daparker2/blastit/FPGA/controller/synthesis/submodules/controller_mm_interconnect_0_rsp_xbar_mux_001.sv

// (C) 2001-2013 Altera Corporation. All rights reserved.
// Your use of Altera Corporation's design tools, logic functions and other 
// software and tools, and its AMPP partner logic functions, and any output 
// files any of the foregoing (including device programming or simulation 
// files), and any associated documentation or information are expressly subject 
// to the terms and conditions of the Altera Program License Subscription 
// Agreement, Altera MegaCore Function License Agreement, or other applicable 
// license agreement, including, without limitation, that your use is for the 
// sole purpose of programming logic devices manufactured by Altera and sold by 
// Altera or its authorized distributors.  Please refer to the applicable 
// agreement for further details.


// $Id: //acds/rel/13.1/ip/merlin/altera_merlin_multiplexer/altera_merlin_multiplexer.sv.terp#1 $
// $Revision: #1 $
// $Date: 2013/08/11 $
// $Author: swbranch $

// ------------------------------------------
// Merlin Multiplexer
// ------------------------------------------

`timescale 1 ns / 1 ns


// ------------------------------------------
// Generation parameters:
//   output_name:         controller_mm_interconnect_0_rsp_xbar_mux_001
//   NUM_INPUTS:          49
//   ARBITRATION_SHARES:  1 1 1 1 1 1 1 1 1 1 1 1 1 1 1 1 1 1 1 1 1 1 1 1 1 1 1 1 1 1 1 1 1 1 1 1 1 1 1 1 1 1 1 1 1 1 1 1 1
//   ARBITRATION_SCHEME   "no-arb"
//   PIPELINE_ARB:        0
//   PKT_TRANS_LOCK:      57 (arbitration locking enabled)
//   ST_DATA_W:           99
//   ST_CHANNEL_W:        49
// ------------------------------------------

module controller_mm_interconnect_0_rsp_xbar_mux_001
(
    // ----------------------
    // Sinks
    // ----------------------
    input                       sink0_valid,
    input [99-1   : 0]  sink0_data,
    input [49-1: 0]  sink0_channel,
    input                       sink0_startofpacket,
    input                       sink0_endofpacket,
    output                      sink0_ready,

    input                       sink1_valid,
    input [99-1   : 0]  sink1_data,
    input [49-1: 0]  sink1_channel,
    input                       sink1_startofpacket,
    input                       sink1_endofpacket,
    output                      sink1_ready,

    input                       sink2_valid,
    input [99-1   : 0]  sink2_data,
    input [49-1: 0]  sink2_channel,
    input                       sink2_startofpacket,
    input                       sink2_endofpacket,
    output                      sink2_ready,

    input                       sink3_valid,
    input [99-1   : 0]  sink3_data,
    input [49-1: 0]  sink3_channel,
    input                       sink3_startofpacket,
    input                       sink3_endofpacket,
    output                      sink3_ready,

    input                       sink4_valid,
    input [99-1   : 0]  sink4_data,
    input [49-1: 0]  sink4_channel,
    input                       sink4_startofpacket,
    input                       sink4_endofpacket,
    output                      sink4_ready,

    input                       sink5_valid,
    input [99-1   : 0]  sink5_data,
    input [49-1: 0]  sink5_channel,
    input                       sink5_startofpacket,
    input                       sink5_endofpacket,
    output                      sink5_ready,

    input                       sink6_valid,
    input [99-1   : 0]  sink6_data,
    input [49-1: 0]  sink6_channel,
    input                       sink6_startofpacket,
    input                       sink6_endofpacket,
    output                      sink6_ready,

    input                       sink7_valid,
    input [99-1   : 0]  sink7_data,
    input [49-1: 0]  sink7_channel,
    input                       sink7_startofpacket,
    input                       sink7_endofpacket,
    output                      sink7_ready,

    input                       sink8_valid,
    input [99-1   : 0]  sink8_data,
    input [49-1: 0]  sink8_channel,
    input                       sink8_startofpacket,
    input                       sink8_endofpacket,
    output                      sink8_ready,

    input                       sink9_valid,
    input [99-1   : 0]  sink9_data,
    input [49-1: 0]  sink9_channel,
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

    input                       sink44_valid,
    input [99-1   : 0]  sink44_data,
    input [49-1: 0]  sink44_channel,
    input                       sink44_startofpacket,
    input                       sink44_endofpacket,
    output                      sink44_ready,

    input                       sink45_valid,
    input [99-1   : 0]  sink45_data,
    input [49-1: 0]  sink45_channel,
    input                       sink45_startofpacket,
    input                       sink45_endofpacket,
    output                      sink45_ready,

    input                       sink46_valid,
    input [99-1   : 0]  sink46_data,
    input [49-1: 0]  sink46_channel,
    input                       sink46_startofpacket,
    input                       sink46_endofpacket,
    output                      sink46_ready,

    input                       sink47_valid,
    input [99-1   : 0]  sink47_data,
    input [49-1: 0]  sink47_channel,
    input                       sink47_startofpacket,
    input                       sink47_endofpacket,
    output                      sink47_ready,

    input                       sink48_valid,
    input [99-1   : 0]  sink48_data,
    input [49-1: 0]  sink48_channel,
    input                       sink48_startofpacket,
    input                       sink48_endofpacket,
    output                      sink48_ready,


    // ----------------------
    // Source
    // ----------------------
    output                      src_valid,
    output [99-1    : 0] src_data,
    output [49-1 : 0] src_channel,
    output                      src_startofpacket,
    output                      src_endofpacket,
    input                       src_ready,

    // ----------------------
    // Clock & Reset
    // ----------------------
    input clk,
    input reset
);
    localparam PAYLOAD_W        = 99 + 49 + 2;
    localparam NUM_INPUTS       = 49;
    localparam SHARE_COUNTER_W  = 1;
    localparam PIPELINE_ARB     = 0;
    localparam ST_DATA_W        = 99;
    localparam ST_CHANNEL_W     = 49;
    localparam PKT_TRANS_LOCK   = 57;

    // ------------------------------------------
    // Signals
    // ------------------------------------------
    wire [NUM_INPUTS - 1 : 0] request;
    wire [NUM_INPUTS - 1 : 0] valid;
    wire [NUM_INPUTS - 1 : 0] grant;
    wire [NUM_INPUTS - 1 : 0] next_grant;
    reg  [NUM_INPUTS - 1 : 0] saved_grant;
    reg  [PAYLOAD_W - 1 : 0]  src_payload;
    wire                      last_cycle;
    reg                       packet_in_progress;
    reg                       update_grant;

    wire [PAYLOAD_W - 1 : 0]  sink0_payload;
    wire [PAYLOAD_W - 1 : 0]  sink1_payload;
    wire [PAYLOAD_W - 1 : 0]  sink2_payload;
    wire [PAYLOAD_W - 1 : 0]  sink3_payload;
    wire [PAYLOAD_W - 1 : 0]  sink4_payload;
    wire [PAYLOAD_W - 1 : 0]  sink5_payload;
    wire [PAYLOAD_W - 1 : 0]  sink6_payload;
    wire [PAYLOAD_W - 1 : 0]  sink7_payload;
    wire [PAYLOAD_W - 1 : 0]  sink8_payload;
    wire [PAYLOAD_W - 1 : 0]  sink9_payload;
    wire [PAYLOAD_W - 1 : 0]  sink10_payload;
    wire [PAYLOAD_W - 1 : 0]  sink11_payload;
    wire [PAYLOAD_W - 1 : 0]  sink12_payload;
    wire [PAYLOAD_W - 1 : 0]  sink13_payload;
    wire [PAYLOAD_W - 1 : 0]  sink14_payload;
    wire [PAYLOAD_W - 1 : 0]  sink15_payload;
    wire [PAYLOAD_W - 1 : 0]  sink16_payload;
    wire [PAYLOAD_W - 1 : 0]  sink17_payload;
    wire [PAYLOAD_W - 1 : 0]  sink18_payload;
    wire [PAYLOAD_W - 1 : 0]  sink19_payload;
    wire [PAYLOAD_W - 1 : 0]  sink20_payload;
    wire [PAYLOAD_W - 1 : 0]  sink21_payload;
    wire [PAYLOAD_W - 1 : 0]  sink22_payload;
    wire [PAYLOAD_W - 1 : 0]  sink23_payload;
    wire [PAYLOAD_W - 1 : 0]  sink24_payload;
    wire [PAYLOAD_W - 1 : 0]  sink25_payload;
    wire [PAYLOAD_W - 1 : 0]  sink26_payload;
    wire [PAYLOAD_W - 1 : 0]  sink27_payload;
    wire [PAYLOAD_W - 1 : 0]  sink28_payload;
    wire [PAYLOAD_W - 1 : 0]  sink29_payload;
    wire [PAYLOAD_W - 1 : 0]  sink30_payload;
    wire [PAYLOAD_W - 1 : 0]  sink31_payload;
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
            share_18 & { SHARE_COUNTER_W {next_grant[18]} } |
            share_19 & { SHARE_COUNTER_W {next_grant[19]} } |
            share_20 & { SHARE_COUNTER_W {next_grant[20]} } |
            share_21 & { SHARE_COUNTER_W {next_grant[21]} } |
            share_22 & { SHARE_COUNTER_W {next_grant[22]} } |
            share_23 & { SHARE_COUNTER_W {next_grant[23]} } |
            share_24 & { SHARE_COUNTER_W {next_grant[24]} } |
            share_25 & { SHARE_COUNTER_W {next_grant[25]} } |
            share_26 & { SHARE_COUNTER_W {next_grant[26]} } |
            share_27 & { SHARE_COUNTER_W {next_grant[27]} } |
            share_28 & { SHARE_COUNTER_W {next_grant[28]} } |
            share_29 & { SHARE_COUNTER_W {next_grant[29]} } |
            share_30 & { SHARE_COUNTER_W {next_grant[30]} } |
            share_31 & { SHARE_COUNTER_W {next_grant[31]} } |
            share_32 & { SHARE_COUNTER_W {next_grant[32]} } |
            share_33 & { SHARE_COUNTER_W {next_grant[33]} } |
            share_34 & { SHARE_COUNTER_W {next_grant[34]} } |
            share_35 & { SHARE_COUNTER_W {next_grant[35]} } |
            share_36 & { SHARE_COUNTER_W {next_grant[36]} } |
            share_37 & { SHARE_COUNTER_W {next_grant[37]} } |
            share_38 & { SHARE_COUNTER_W {next_grant[38]} } |
            share_39 & { SHARE_COUNTER_W {next_grant[39]} } |
            share_40 & { SHARE_COUNTER_W {next_grant[40]} } |
            share_41 & { SHARE_COUNTER_W {next_grant[41]} } |
            share_42 & { SHARE_COUNTER_W {next_grant[42]} } |
            share_43 & { SHARE_COUNTER_W {next_grant[43]} } |
            share_44 & { SHARE_COUNTER_W {next_grant[44]} } |
            share_45 & { SHARE_COUNTER_W {next_grant[45]} } |
            share_46 & { SHARE_COUNTER_W {next_grant[46]} } |
            share_47 & { SHARE_COUNTER_W {next_grant[47]} } |
            share_48 & { SHARE_COUNTER_W {next_grant[48]} };
    end

    // ------------------------------------------
    // Flag to indicate first packet of an arb sequence.
    // ------------------------------------------
    wire grant_changed = ~packet_in_progress && ~(|(saved_grant & valid));
    reg first_packet_r;
    wire first_packet = grant_changed | first_packet_r;
    always @(posedge clk or posedge reset) begin
        if (reset) begin
            first_packet_r <= 1'b0;
        end
        else begin 
            if (update_grant)
                first_packet_r <= 1'b1;
            else if (last_cycle)
                first_packet_r <= 1'b0;
            else if (grant_changed)
                first_packet_r <= 1'b1;
        end
    end

    // ------------------------------------------
    // Compute the next share-count value.
    // ------------------------------------------
    reg [SHARE_COUNTER_W - 1 : 0] p1_share_count;
    reg [SHARE_COUNTER_W - 1 : 0] share_count;
    reg share_count_zero_flag;

    always @* begin
        if (first_packet) begin
            p1_share_count = next_grant_share;
        end
        else begin
            // Update the counter, but don't decrement below 0.
            p1_share_count = share_count_zero_flag ? '0 : share_count - 1'b1;
        end
    end

    // ------------------------------------------
    // Update the share counter and share-counter=zero flag.
    // ------------------------------------------
    always @(posedge clk or posedge reset) begin
        if (reset) begin
            share_count <= '0;
            share_count_zero_flag <= 1'b1;
        end
        else begin
            if (last_cycle) begin
                share_count <= p1_share_count;
                share_count_zero_flag <= (p1_share_count == '0);
            end
        end
    end

    // ------------------------------------------
    // For each input, maintain a final_packet signal which goes active for the
    // last packet of a full-share packet sequence.  Example: if I have 4
    // shares and I'm continuously requesting, final_packet is active in the
    // 4th packet.
    // ------------------------------------------
    wire final_packet_0 = 1'b1;

    wire final_packet_1 = 1'b1;

    wire final_packet_2 = 1'b1;

    wire final_packet_3 = 1'b1;

    wire final_packet_4 = 1'b1;

    wire final_packet_5 = 1'b1;

    wire final_packet_6 = 1'b1;

    wire final_packet_7 = 1'b1;

    wire final_packet_8 = 1'b1;

    wire final_packet_9 = 1'b1;

    wire final_packet_10 = 1'b1;

    wire final_packet_11 = 1'b1;

    wire final_packet_12 = 1'b1;

    wire final_packet_13 = 1'b1;

    wire final_packet_14 = 1'b1;

    wire final_packet_15 = 1'b1;

    wire final_packet_16 = 1'b1;

    wire final_packet_17 = 1'b1;

    wire final_packet_18 = 1'b1;

    wire final_packet_19 = 1'b1;

    wire final_packet_20 = 1'b1;

    wire final_packet_21 = 1'b1;

    wire final_packet_22 = 1'b1;

    wire final_packet_23 = 1'b1;

    wire final_packet_24 = 1'b1;

    wire final_packet_25 = 1'b1;

    wire final_packet_26 = 1'b1;

    wire final_packet_27 = 1'b1;

    wire final_packet_28 = 1'b1;

    wire final_packet_29 = 1'b1;

    wire final_packet_30 = 1'b1;

    wire final_packet_31 = 1'b1;

    wire final_packet_32 = 1'b1;

    wire final_packet_33 = 1'b1;

    wire final_packet_34 = 1'b1;

    wire final_packet_35 = 1'b1;

    wire final_packet_36 = 1'b1;

    wire final_packet_37 = 1'b1;

    wire final_packet_38 = 1'b1;

    wire final_packet_39 = 1'b1;

    wire final_packet_40 = 1'b1;

    wire final_packet_41 = 1'b1;

    wire final_packet_42 = 1'b1;

    wire final_packet_43 = 1'b1;

    wire final_packet_44 = 1'b1;

    wire final_packet_45 = 1'b1;

    wire final_packet_46 = 1'b1;

    wire final_packet_47 = 1'b1;

    wire final_packet_48 = 1'b1;


    // ------------------------------------------
    // Concatenate all final_packet signals (wire or reg) into a handy vector.
    // ------------------------------------------
    wire [NUM_INPUTS - 1 : 0] final_packet = {
        final_packet_48,
        final_packet_47,
        final_packet_46,
        final_packet_45,
        final_packet_44,
        final_packet_43,
        final_packet_42,
        final_packet_41,
        final_packet_40,
        final_packet_39,
        final_packet_38,
        final_packet_37,
        final_packet_36,
        final_packet_35,
        final_packet_34,
        final_packet_33,
        final_packet_32,
        final_packet_31,
        final_packet_30,
        final_packet_29,
        final_packet_28,
        final_packet_27,
        final_packet_26,
        final_packet_25,
        final_packet_24,
        final_packet_23,
        final_packet_22,
        final_packet_21,
        final_packet_20,
        final_packet_19,
        final_packet_18,
        final_packet_17,
        final_packet_16,
        final_packet_15,
        final_packet_14,
        final_packet_13,
        final_packet_12,
        final_packet_11,
        final_packet_10,
        final_packet_9,
        final_packet_8,
        final_packet_7,
        final_packet_6,
        final_packet_5,
        final_packet_4,
        final_packet_3,
        final_packet_2,
        final_packet_1,
        final_packet_0
    };

    // ------------------------------------------
    // ------------------------------------------
    wire p1_done = |(final_packet & grant);

    // ------------------------------------------
    // Flag for the first cycle of packets within an 
    // arb sequence
    // ------------------------------------------
    reg first_cycle;
    always @(posedge clk, posedge reset) begin
        if (reset)
            first_cycle <= 0;
        else
            first_cycle <= last_cycle && ~p1_done;
    end


    always @* begin
        update_grant = 0;

        // ------------------------------------------
        // No arbitration pipeline, update grant whenever
        // the current arb winner has consumed all shares,
        // or all requests are low
        // ------------------------------------------
        update_grant = (last_cycle && p1_done) || (first_cycle && ~(|valid));
        update_grant = last_cycle;
    end

    wire save_grant;
    assign save_grant = 1;
    assign grant      = next_grant;

    always @(posedge clk, posedge reset) begin
        if (reset)
            saved_grant <= '0;
        else if (save_grant)
            saved_grant <= next_grant;
    end

    // ------------------------------------------
    // ------------------------------------------
    // Arbitrator
    // ------------------------------------------
    // ------------------------------------------

    // ------------------------------------------
    // Create a request vector that stays high during
    // the packet for unpipelined arbitration.
    //
    // The pipelined arbitration scheme does not require
    // request to be held high during the packet.
    // ------------------------------------------
    assign request = valid;


    altera_merlin_arbitrator
    #(
        .NUM_REQUESTERS(NUM_INPUTS),
        .SCHEME        ("no-arb"),
        .PIPELINE      (0)
    ) arb (
        .clk                    (clk),
        .reset                  (reset),
        .request                (request),
        .grant                  (next_grant),
        .save_top_priority      (src_valid),
        .increment_top_priority (update_grant)
    );

    // ------------------------------------------
    // ------------------------------------------
    // Mux
    //
    // Implemented as a sum of products.
    // ------------------------------------------
    // ------------------------------------------

    assign sink0_ready = src_ready && grant[0];
    assign sink1_ready = src_ready && grant[1];
    assign sink2_ready = src_ready && grant[2];
    assign sink3_ready = src_ready && grant[3];
    assign sink4_ready = src_ready && grant[4];
    assign sink5_ready = src_ready && grant[5];
    assign sink6_ready = src_ready && grant[6];
    assign sink7_ready = src_ready && grant[7];
    assign sink8_ready = src_ready && grant[8];
    assign sink9_ready = src_ready && grant[9];
    assign sink10_ready = src_ready && grant[10];
    assign sink11_ready = src_ready && grant[11];
    assign sink12_ready = src_ready && grant[12];
    assign sink13_ready = src_ready && grant[13];
    assign sink14_ready = src_ready && grant[14];
    assign sink15_ready = src_ready && grant[15];
    assign sink16_ready = src_ready && grant[16];
    assign sink17_ready = src_ready && grant[17];
    assign sink18_ready = src_ready && grant[18];
    assign sink19_ready = src_ready && grant[19];
    assign sink20_ready = src_ready && grant[20];
    assign sink21_ready = src_ready && grant[21];
    assign sink22_ready = src_ready && grant[22];
    assign sink23_ready = src_ready && grant[23];
    assign sink24_ready = src_ready && grant[24];
    assign sink25_ready = src_ready && grant[25];
    assign sink26_ready = src_ready && grant[26];
    assign sink27_ready = src_ready && grant[27];
    assign sink28_ready = src_ready && grant[28];
    assign sink29_ready = src_ready && grant[29];
    assign sink30_ready = src_ready && grant[30];
    assign sink31_ready = src_ready && grant[31];
    assign sink32_ready = src_ready && grant[32];
    assign sink33_ready = src_ready && grant[33];
    assign sink34_ready = src_ready && grant[34];
    assign sink35_ready = src_ready && grant[35];
    assign sink36_ready = src_ready && grant[36];
    assign sink37_ready = src_ready && grant[37];
    assign sink38_ready = src_ready && grant[38];
    assign sink39_ready = src_ready && grant[39];
    assign sink40_ready = src_ready && grant[40];
    assign sink41_ready = src_ready && grant[41];
    assign sink42_ready = src_ready && grant[42];
    assign sink43_ready = src_ready && grant[43];
    assign sink44_ready = src_ready && grant[44];
    assign sink45_ready = src_ready && grant[45];
    assign sink46_ready = src_ready && grant[46];
    assign sink47_ready = src_ready && grant[47];
    assign sink48_ready = src_ready && grant[48];

    assign src_valid = |(grant & valid);

    always @* begin
        src_payload =
            sink0_payload & {PAYLOAD_W {grant[0]} } |
            sink1_payload & {PAYLOAD_W {grant[1]} } |
            sink2_payload & {PAYLOAD_W {grant[2]} } |
            sink3_payload & {PAYLOAD_W {grant[3]} } |
            sink4_payload & {PAYLOAD_W {grant[4]} } |
            sink5_payload & {PAYLOAD_W {grant[5]} } |
            sink6_payload & {PAYLOAD_W {grant[6]} } |
            sink7_payload & {PAYLOAD_W {grant[7]} } |
            sink8_payload & {PAYLOAD_W {grant[8]} } |
            sink9_payload & {PAYLOAD_W {grant[9]} } |
            sink10_payload & {PAYLOAD_W {grant[10]} } |
            sink11_payload & {PAYLOAD_W {grant[11]} } |
            sink12_payload & {PAYLOAD_W {grant[12]} } |
            sink13_payload & {PAYLOAD_W {grant[13]} } |
            sink14_payload & {PAYLOAD_W {grant[14]} } |
            sink15_payload & {PAYLOAD_W {grant[15]} } |
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
        sink47_startofpacket,sink47_endofpacket};
    assign sink48_payload = {sink48_channel,sink48_data,
        sink48_startofpacket,sink48_endofpacket};

    assign {src_channel,src_data,src_startofpacket,src_endofpacket} = src_payload;
endmodule
