daparker2/blastit/FPGA/controller/synthesis/submodules/controller_uart1_tx_counter.v

//Legal Notice: (C)2018 Altera Corporation. All rights reserved.  Your
//use of Altera Corporation's design tools, logic functions and other
//software and tools, and its AMPP partner logic functions, and any
//output files any of the foregoing (including device programming or
//simulation files), and any associated documentation or information are
//expressly subject to the terms and conditions of the Altera Program
//License Subscription Agreement or other applicable license agreement,
//including, without limitation, that your use is for the sole purpose
//of programming logic devices manufactured by Altera and sold by Altera
//or its authorized distributors.  Please refer to the applicable
//agreement for further details.

// synthesis translate_off
`timescale 1ns / 1ps
// synthesis translate_on

// turn off superfluous verilog processor warnings 
// altera message_level Level1 
// altera message_off 10034 10035 10036 10037 10230 10240 10030 

module controller_uart1_tx_counter (
                                     // inputs:
                                      address,
                                      chipselect,
                                      clk,
                                      in_port,
                                      reset_n,
                                      write_n,
                                      writedata,

                                     // outputs:
                                      readdata
                                   )
;

  output  [ 31: 0] readdata;
  input   [  1: 0] address;
  input            chipselect;
  input            clk;
  input   [  2: 0] in_port;
  input            reset_n;
  input            write_n;
  input   [ 31: 0] writedata;

  wire             clk_en;
  reg     [  2: 0] d1_data_in;
  reg     [  2: 0] d2_data_in;
  wire    [  2: 0] data_in;
  reg     [  2: 0] edge_capture;
  wire             edge_capture_wr_strobe;
  wire    [  2: 0] edge_detect;
  wire    [  2: 0] read_mux_out;
  reg     [ 31: 0] readdata;
  assign clk_en = 1;
  //s1, which is an e_avalon_slave
  assign read_mux_out = ({3 {(address == 0)}} & data_in) |
    ({3 {(address == 3)}} & edge_capture);

  always @(posedge clk or negedge reset_n)
    begin
      if (reset_n == 0)
          readdata <= 0;
      else if (clk_en)
          readdata <= {32'b0 | read_mux_out};
    end


  assign data_in = in_port;
  assign edge_capture_wr_strobe = chipselect && ~write_n && (address == 3);
  always @(posedge clk or negedge reset_n)
    begin
      if (reset_n == 0)
          edge_capture[0] <= 0;
      else if (clk_en)
          if (edge_capture_wr_strobe)
              edge_capture[0] <= 0;
          else if (edge_detect[0])
              edge_capture[0] <= -1;
    end


  always @(posedge clk or negedge reset_n)
    begin
      if (reset_n == 0)
          edge_capture[1] <= 0;
      else if (clk_en)
          if (edge_capture_wr_strobe)
              edge_capture[1] <= 0;
          else if (edge_detect[1])
              edge_capture[1] <= -1;
    end


  always @(posedge clk or negedge reset_n)
    begin
      if (reset_n == 0)
          edge_capture[2] <= 0;
      else if (clk_en)
          if (edge_capture_wr_strobe)
              edge_capture[2] <= 0;
          else if (edge_detect[2])
              edge_capture[2] <= -1;
    end


  always @(posedge clk or negedge reset_n)
    begin
      if (reset_n == 0)
        begin
          d1_data_in <= 0;
          d2_data_in <= 0;
        end
      else if (clk_en)
        begin
          d1_data_in <= data_in;
          d2_data_in <= d1_data_in;
        end
    end


  assign edge_detect = d1_data_in & ~d2_data_in;

endmodule
